Atharv-Shukla-987/KeyBoard/img/Case_bottom.png

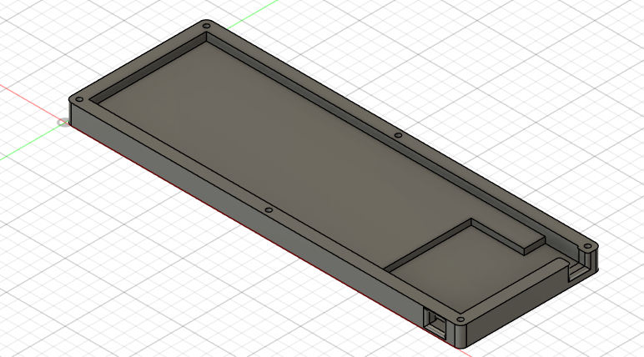
img/Case_bottom.png
