Atharv-Shukla-987/KeyBoard/img/Case_top.png

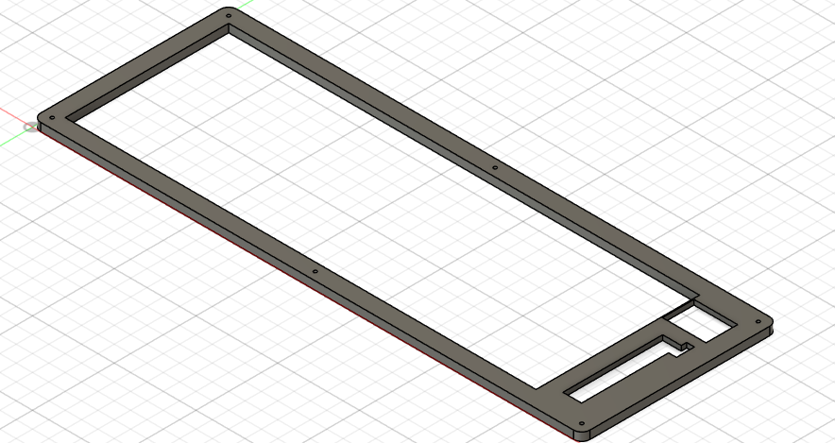
img/Case_top.png
