Atharv-Shukla-987/KeyBoard/img/keyboard_3d_back.png

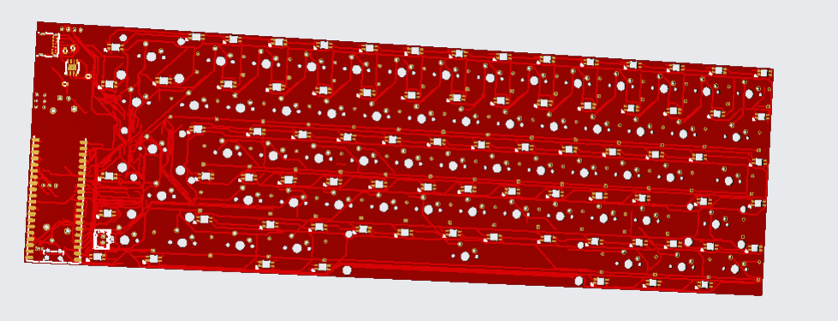
img/keyboard_3d_back.png
