Atharv-Shukla-987/KeyBoard/img/keyboard_pcb_withslikscreen.png

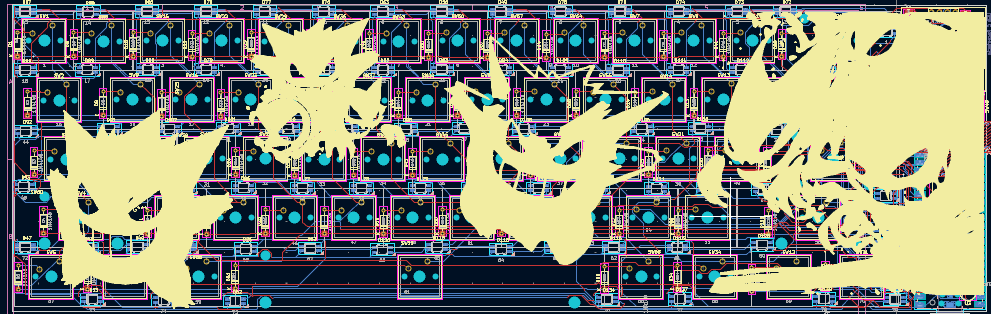
img/keyboard_pcb_withslikscreen.png
