Atharv-Shukla-987/KeyBoard/img/reciever_pcb.png

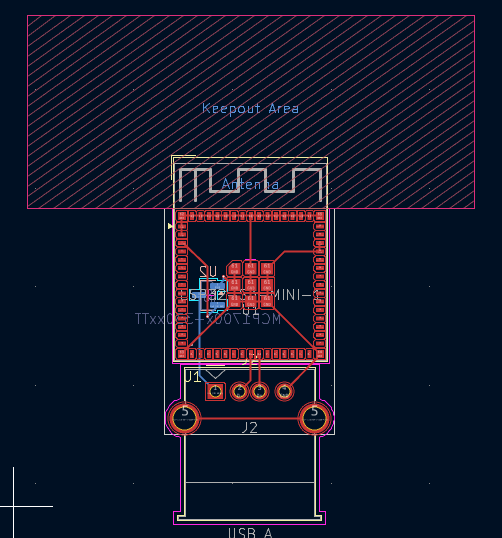
img/reciever_pcb.png
