Atharv-Shukla-987/KeyBoard/img/Screenshot 2026-06-04 075334.png

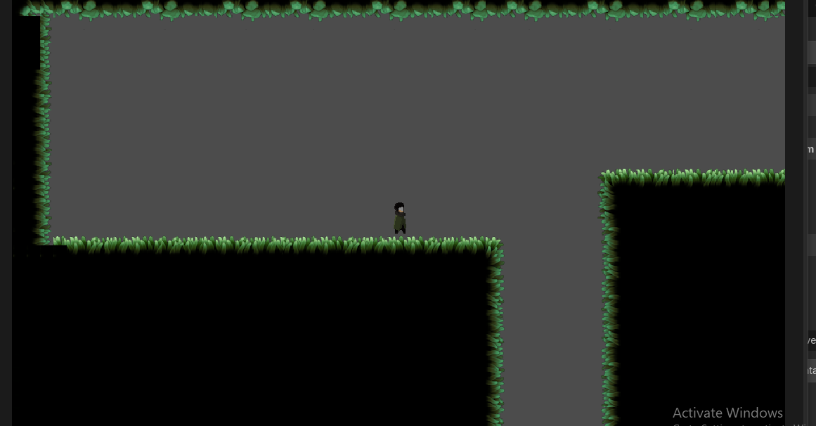
img/Screenshot 2026-06-04 075334.png
