Atharv-Shukla-987/KeyBoard/img/bom.png

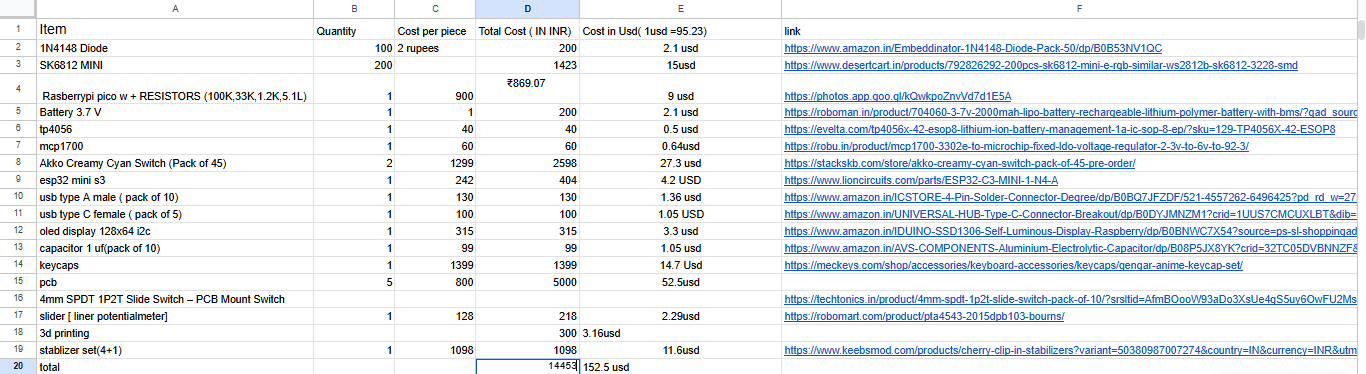
img/bom.png
