Atharv-Shukla-987/KeyBoard/img/Assembly.png

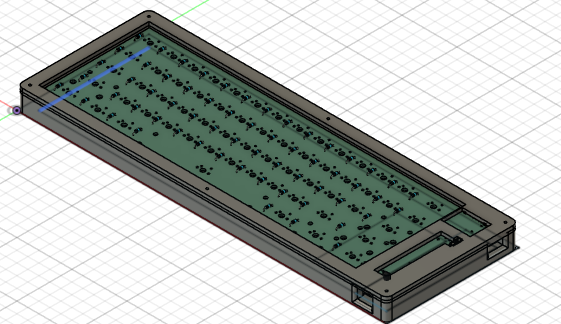
img/Assembly.png
